goncalomb/scale2pos/src/utils/bootstrap.py

import asyncio
import time

import machine

from utils.led import led_force, led_force_toggle, led_state

_t_load = time.ticks_ms()
_t_boot = 0
_t_main = 0

print('load')


def run(main, *, led=True, wdt=True, handle_exceptions=True, reset=True):
    global _t_boot
    _t_boot = time.ticks_ms()

    print('boot')

    async def boot():
        if wdt:
            async def feed(wdt: machine.WDT):
                while True:
                    wdt.feed()
                    await asyncio.sleep_ms(500)
            # on rp2040 the max timeout is 8388
            asyncio.create_task(feed(machine.WDT(timeout=8388)))

        if handle_exceptions:
            # XXX: kill the loop by re-raising the exception
            # this a bit overkill and does not cancel any pending tasks
            # no public function to fetch all tasks? research more?
            def kill_handler(loop, context):
                print('kill')
                raise context['exception']
            asyncio.get_event_loop().set_exception_handler(kill_handler)

        async def print_timings():
            now = time.ticks_ms()
            print(
                'timings:',
                _t_boot - _t_load, _t_main - _t_boot, now - _t_main,
                '[load] [boot] [main]',
            )
        asyncio.create_task(print_timings())

        if led:
            led_state()
        global _t_main
        _t_main = time.ticks_ms()
        await main

    try:
        if led:
            led_force()
        asyncio.run(boot())
        if reset:
            machine.soft_reset()
    finally:
        if led:
            led_force(False)
        print('end')


def panic(msg=None, *, led=True):
    msg = 'panic: ' + msg if msg else 'panic'
    while True:
        print(msg)
        if led:
            for _ in range(50):
                led_force_toggle()
                time.sleep_ms(100)
        else:
            time.sleep_ms(5000)
